fbelavenuto/TK90X-PCB/Rev5/Docs/roteada2.pdf

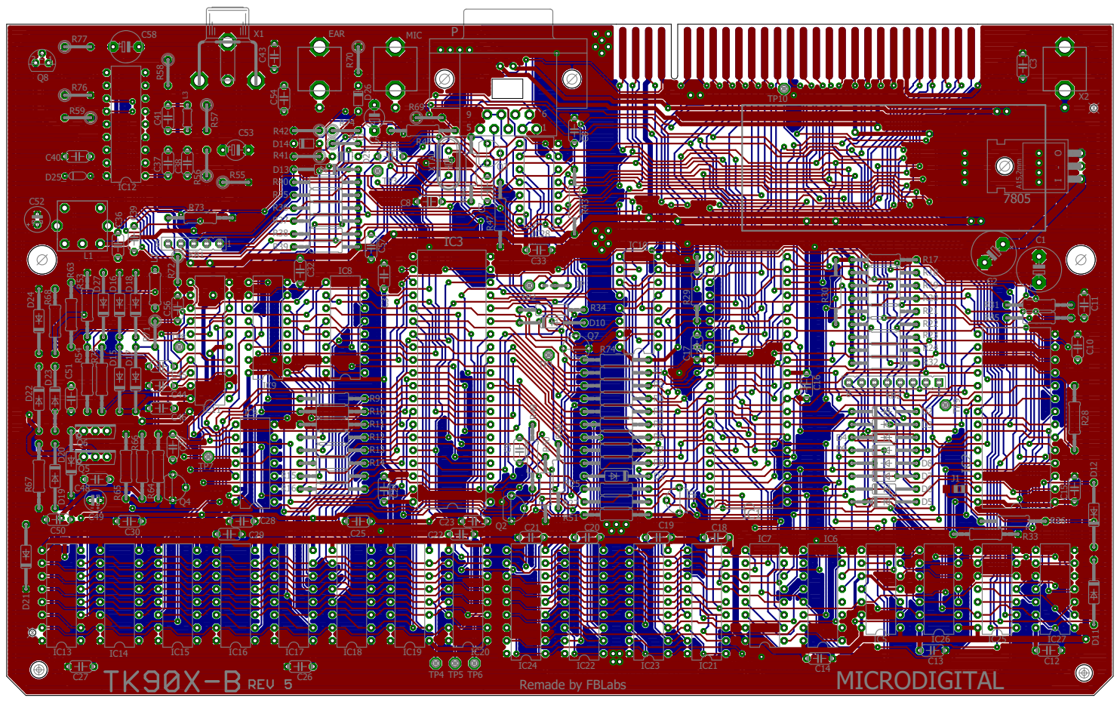
[picture p12: page 1]
