fbelavenuto/TK90X-PCB/Rev3/Docs/mapa_completo.pdf

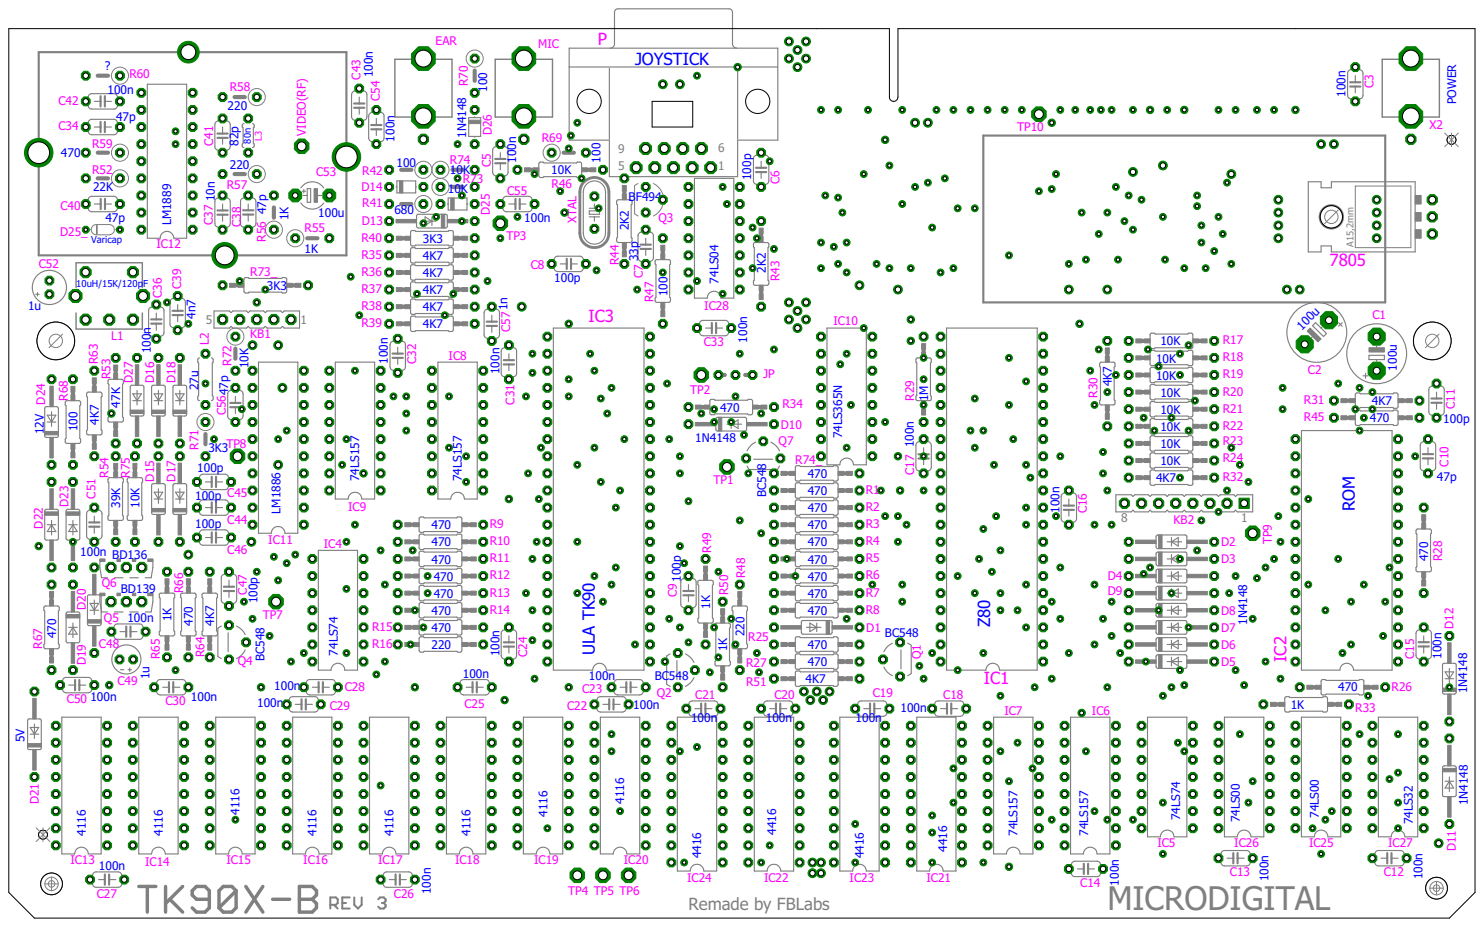
[picture p13: page 1]
