fbelavenuto/TK90X-PCB/Rev4/Docs/mapa_completo.pdf

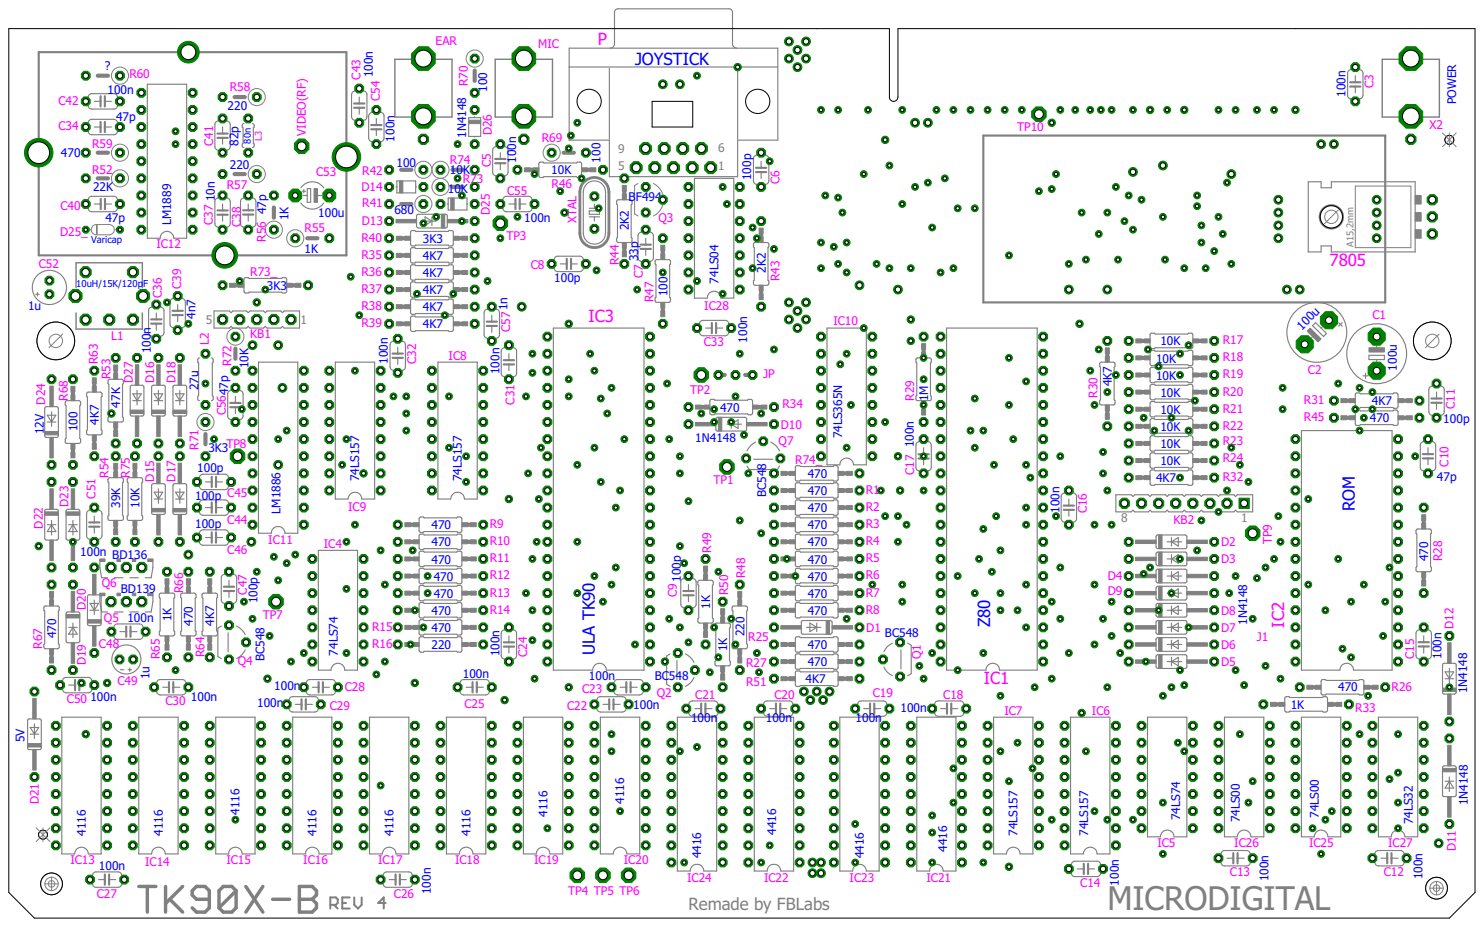
[picture p14: page 1]
