fbelavenuto/TK90X-PCB/Rev5/Docs/mapa_completo.pdf

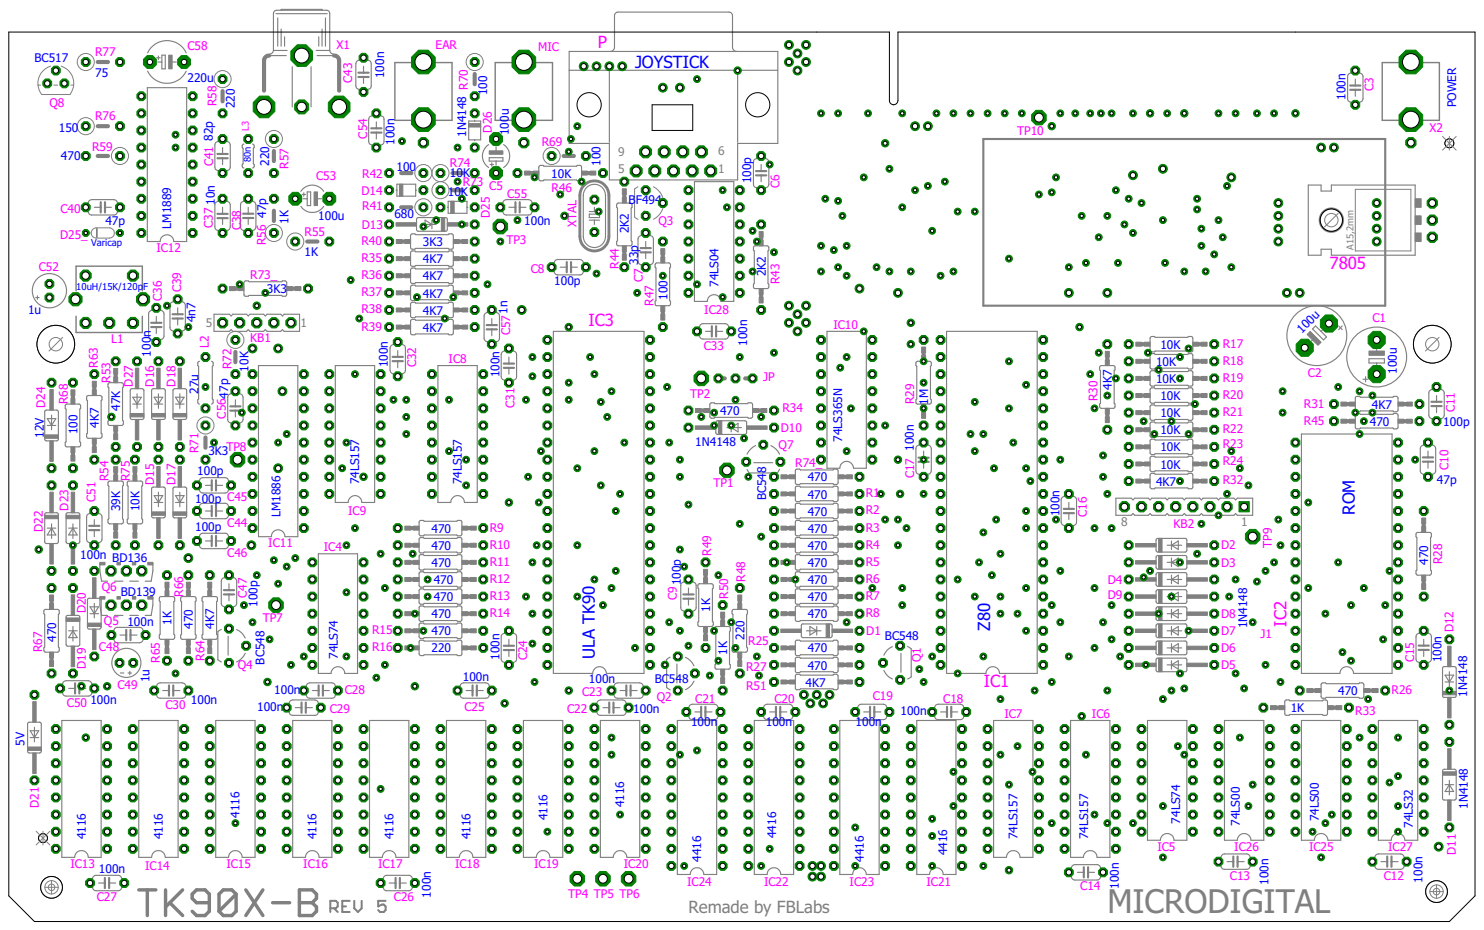
[picture p15: page 1]
